Keenan-sad/terrarium-hardware/controller/pcb/image/v1.1_front.jpg

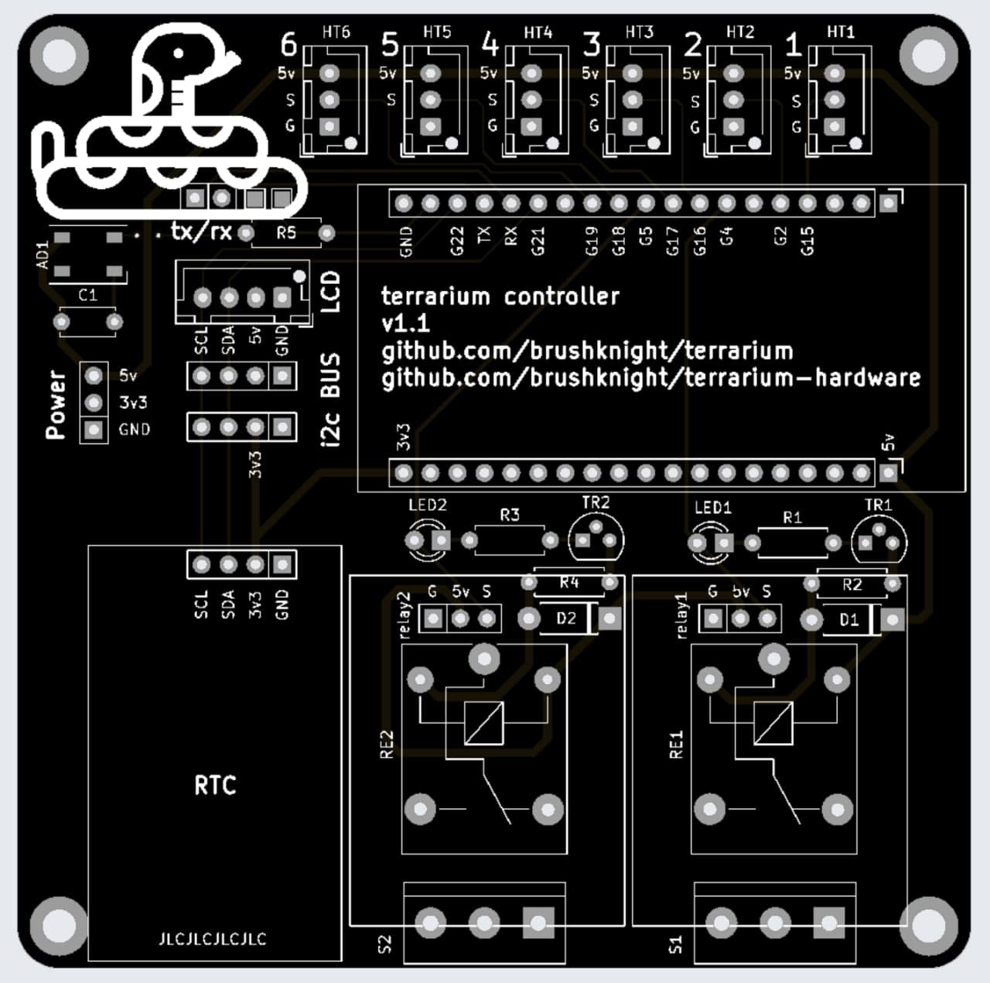
controller/pcb/image/v1.1_front.jpg
