Keenan-sad/terrarium-hardware/controller/pcb/image/v1.2_back.png

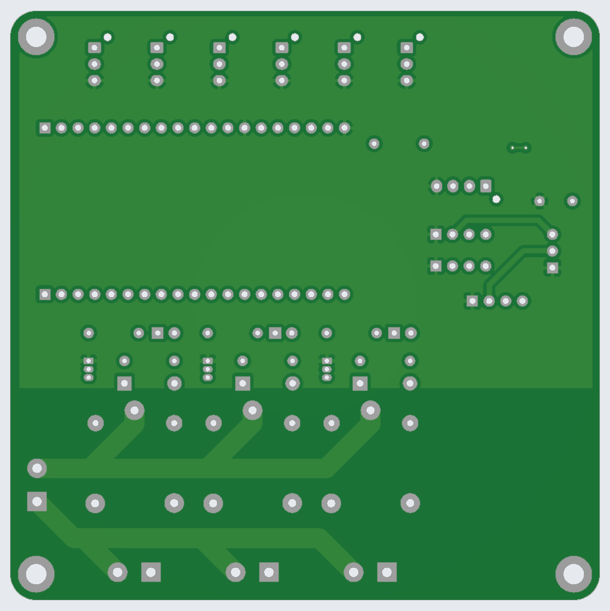
controller/pcb/image/v1.2_back.png
