Keenan-sad/terrarium-hardware/screen/back lid.stl

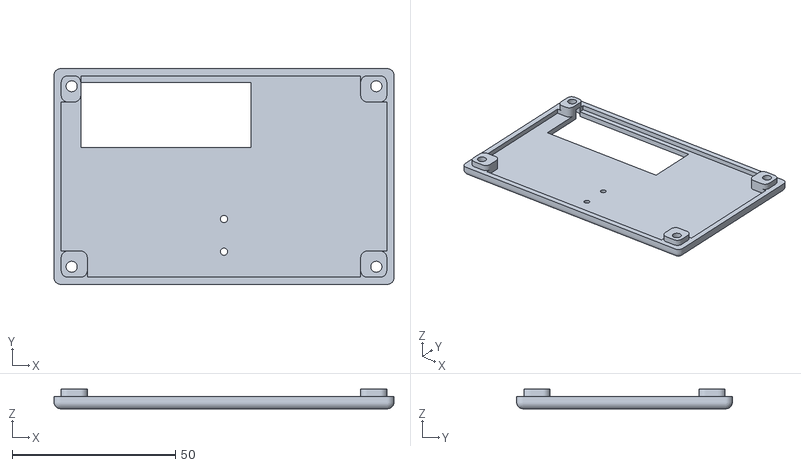
[picture p25: CAD file, 2021-11-30]
screen/back lid.stl
104.0 x 66.0 x 6.00
