Keenan-sad/terrarium-hardware/controller/pcb/models/Screw Terminal Block 5mm 2-way.step

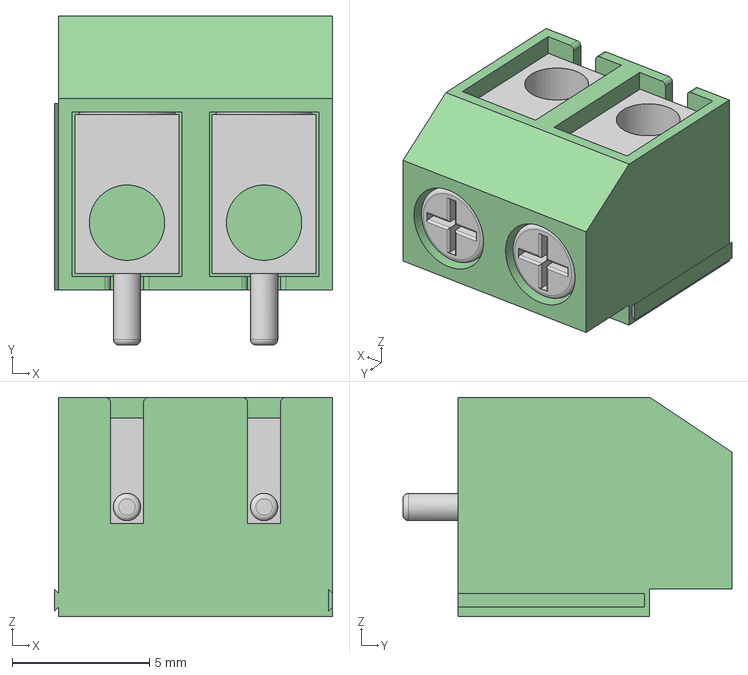
[picture p26: CAD file, 2022-01-11]
controller/pcb/models/Screw Terminal Block 5mm 2-way.step
10.2 x 12.0 x 8.00 mm
